tuna-f1sh/wire-dispenser/img/IMG_0899.JPG

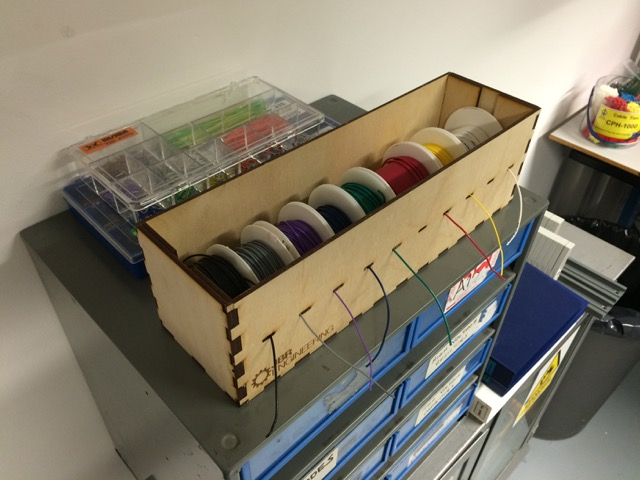
img/IMG_0899.JPG
